bvavra/MIDI_Accordion/Prototypes/Bluetooth/Bluetooth_Tutorial/bluetooth_schematic_1.GIF

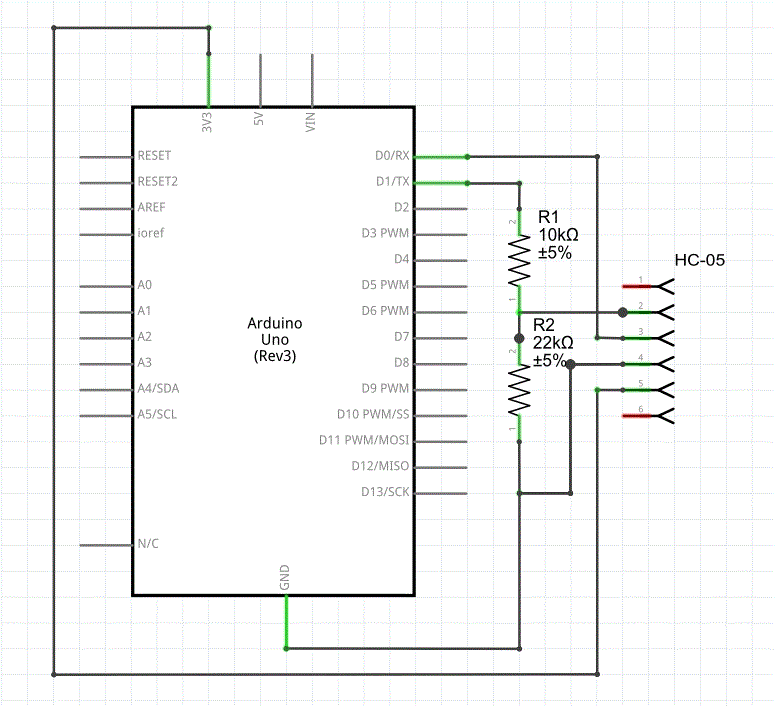
Prototypes/Bluetooth/Bluetooth_Tutorial/bluetooth_schematic_1.GIF
