bvavra/MIDI_Accordion/Prototypes/Opto_Interruptor/Opto_Interruptor_1/working_output.gif

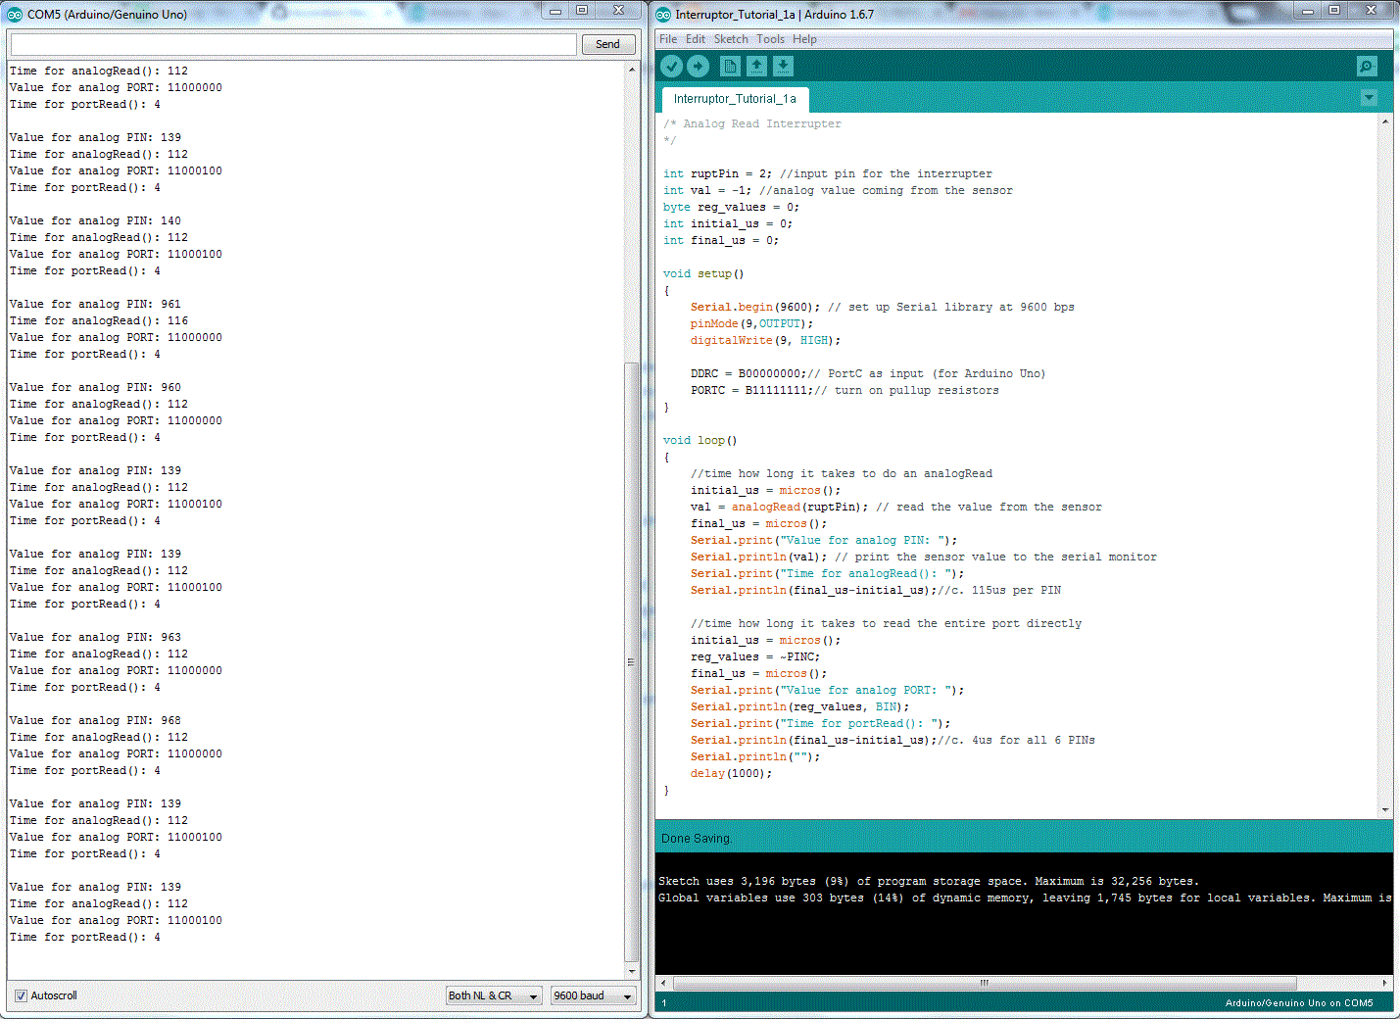
Prototypes/Opto_Interruptor/Opto_Interruptor_1/working_output.gif
