bvavra/MIDI_Accordion/Prototypes/Opto_Interruptor/Opto_Interruptor_1/working_single_analog.GIF

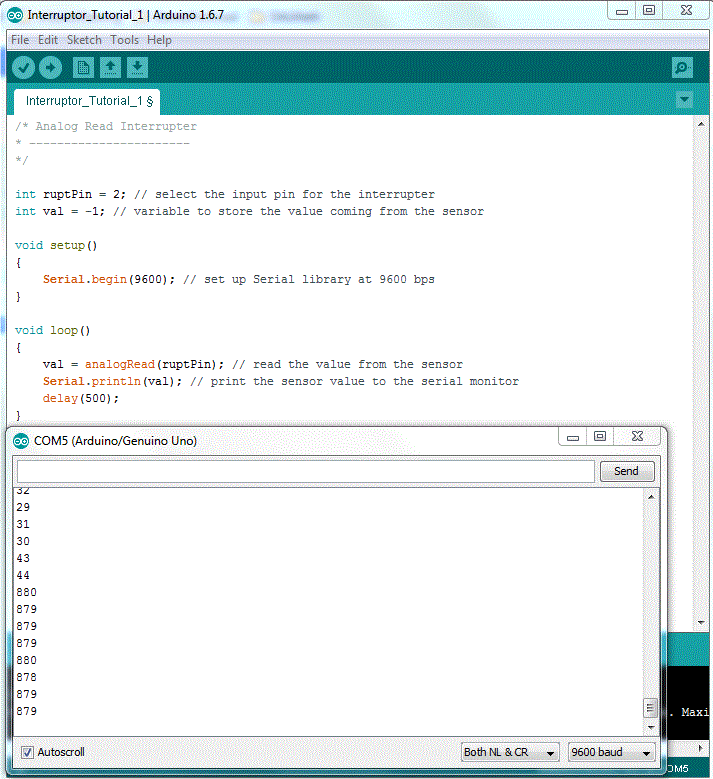
Prototypes/Opto_Interruptor/Opto_Interruptor_1/working_single_analog.GIF
