bvavra/MIDI_Accordion/Prototypes/Bluetooth/Bluetooth_Tutorial/bluetooth_fig1_serial.GIF

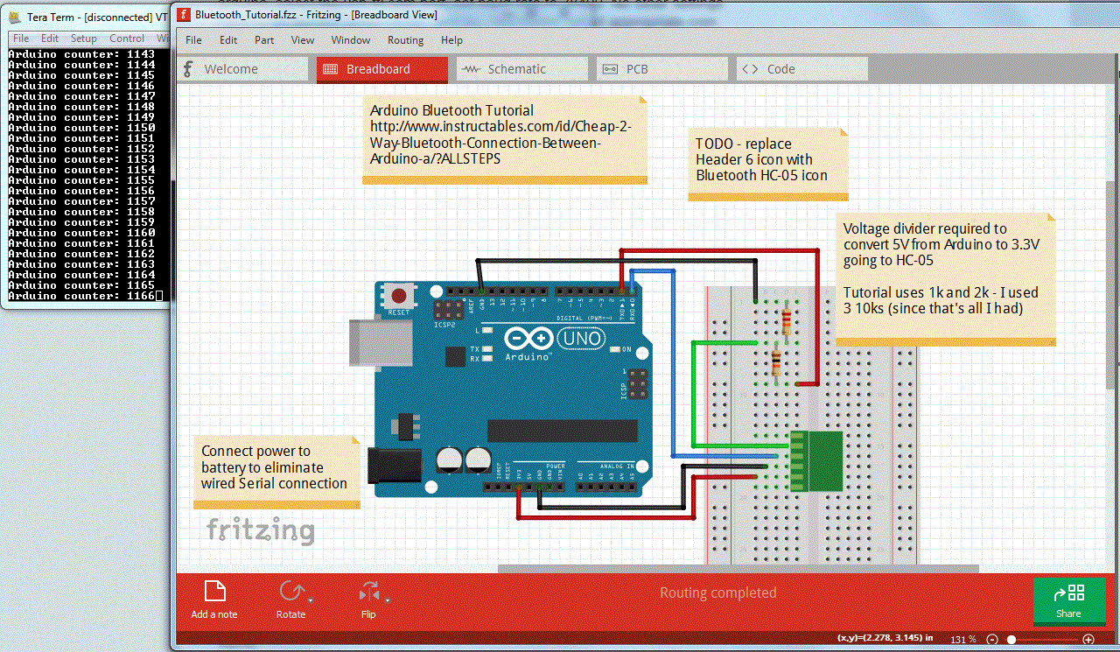
Prototypes/Bluetooth/Bluetooth_Tutorial/bluetooth_fig1_serial.GIF
