bvavra/MIDI_Accordion/Prototypes/Bluetooth/Bluetooth_Tutorial/bluetooth_fig1b_arduino.jpg

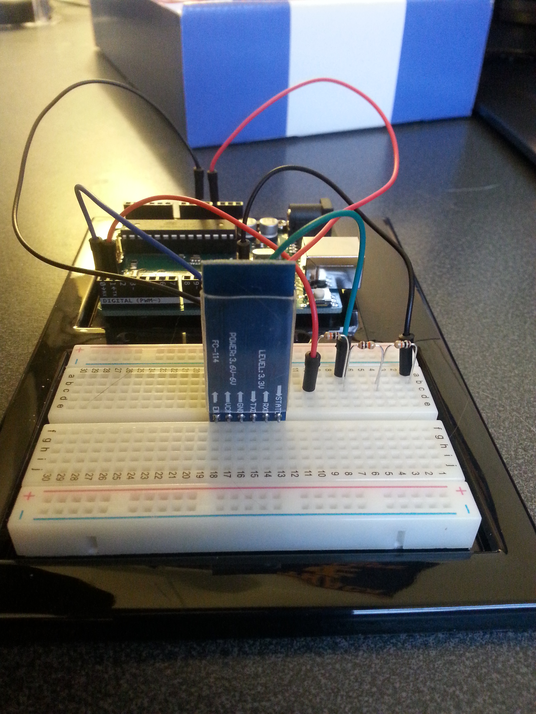
Prototypes/Bluetooth/Bluetooth_Tutorial/bluetooth_fig1b_arduino.jpg
