bvavra/MIDI_Accordion/Prototypes/Bluetooth/Bluetooth_Tutorial_2/bluetooth_fig2_midi.GIF

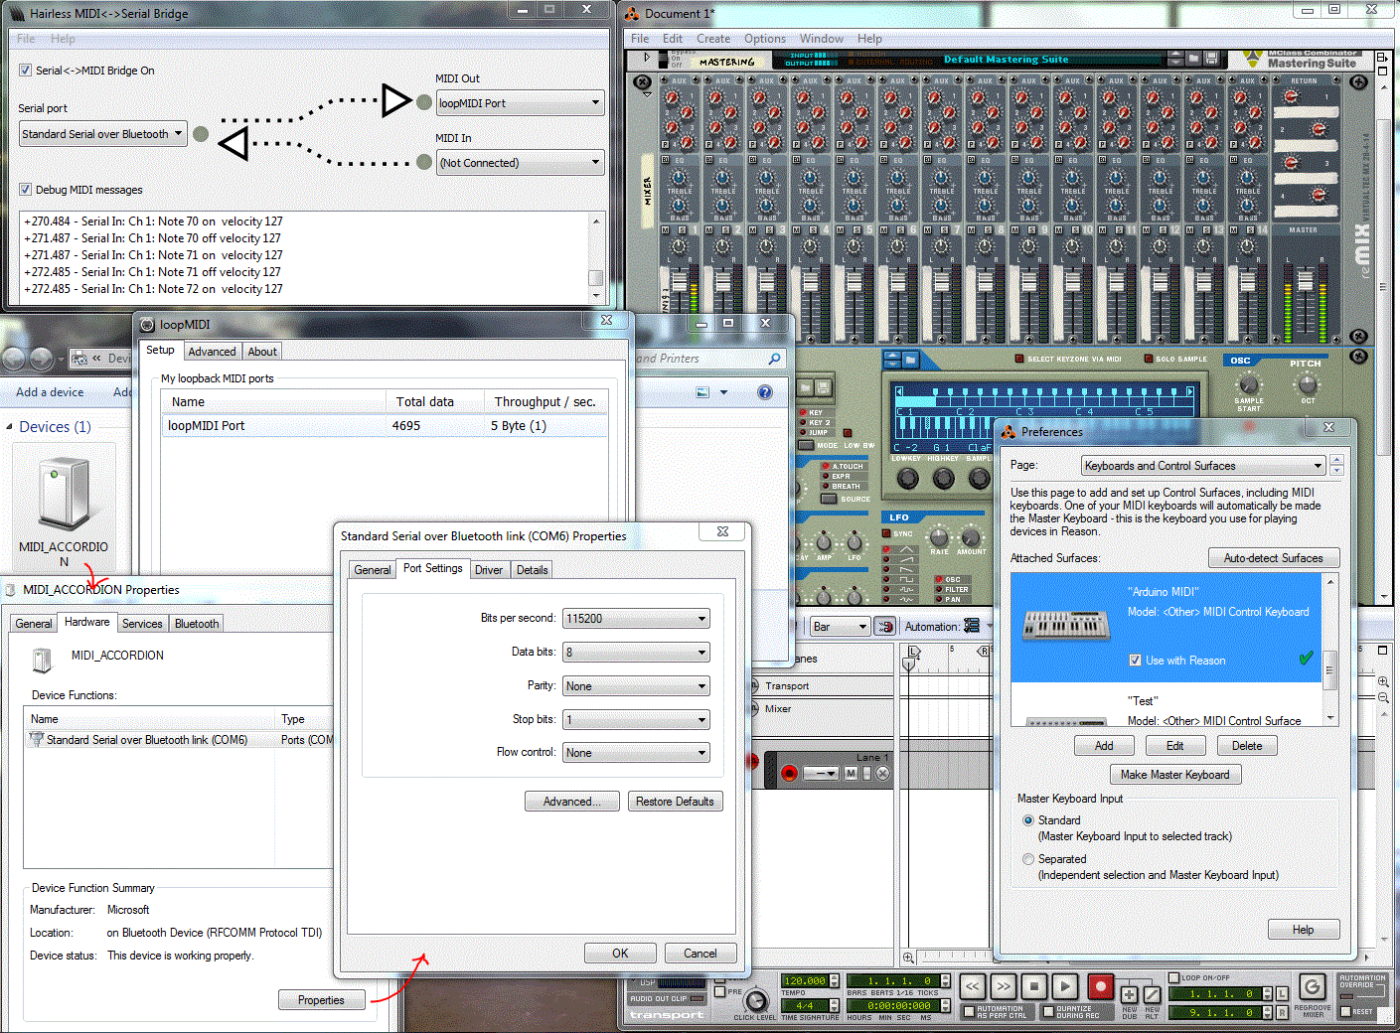
Prototypes/Bluetooth/Bluetooth_Tutorial_2/bluetooth_fig2_midi.GIF
