bvavra/MIDI_Accordion/Prototypes/Bluetooth/Bluetooth_Tutorial_2/bluetooth_fig2a_arduino.jpg

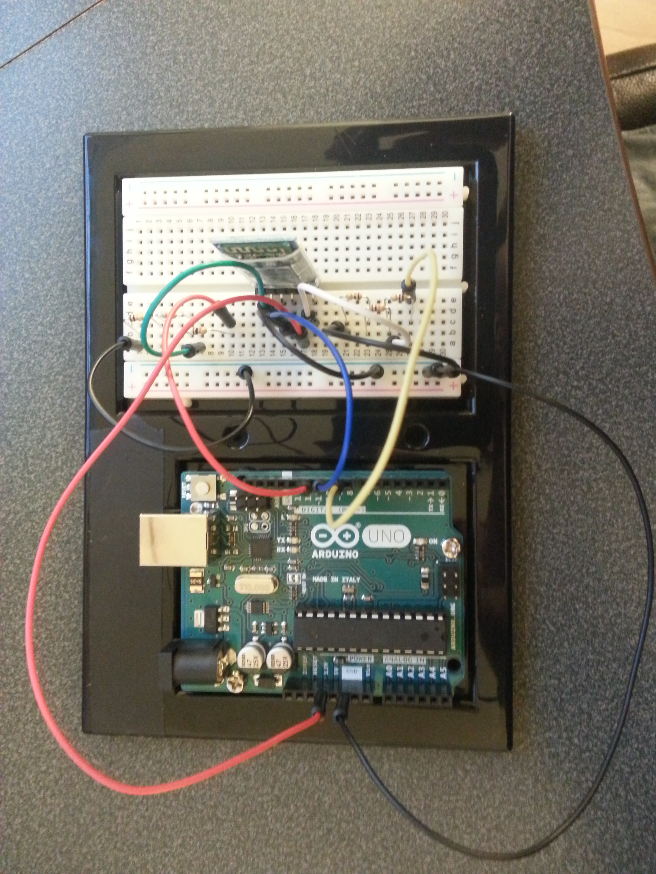
Prototypes/Bluetooth/Bluetooth_Tutorial_2/bluetooth_fig2a_arduino.jpg
