bvavra/MIDI_Accordion/Prototypes/MIDI_Tutorial/midi_fig2_serial_to_midi.GIF

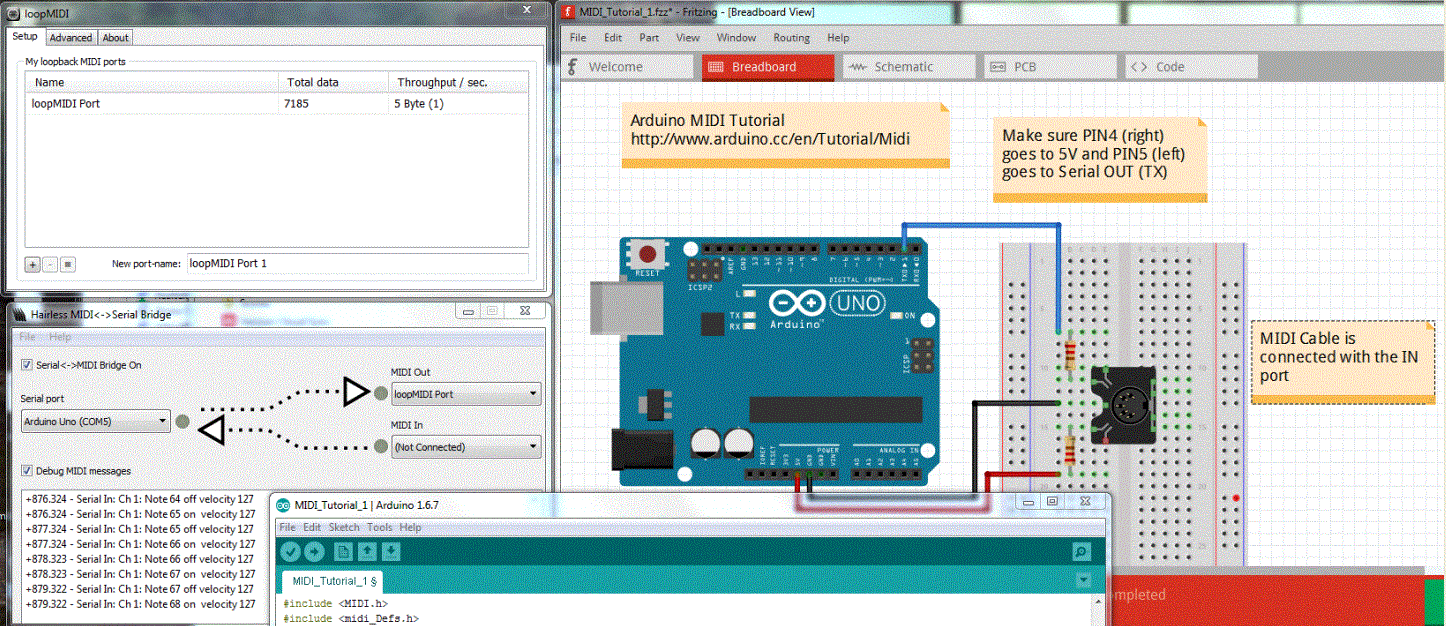
Prototypes/MIDI_Tutorial/midi_fig2_serial_to_midi.GIF
