bvavra/MIDI_Accordion/Prototypes/MIDI_Tutorial/midi_fig3_arduino_to_reason.GIF

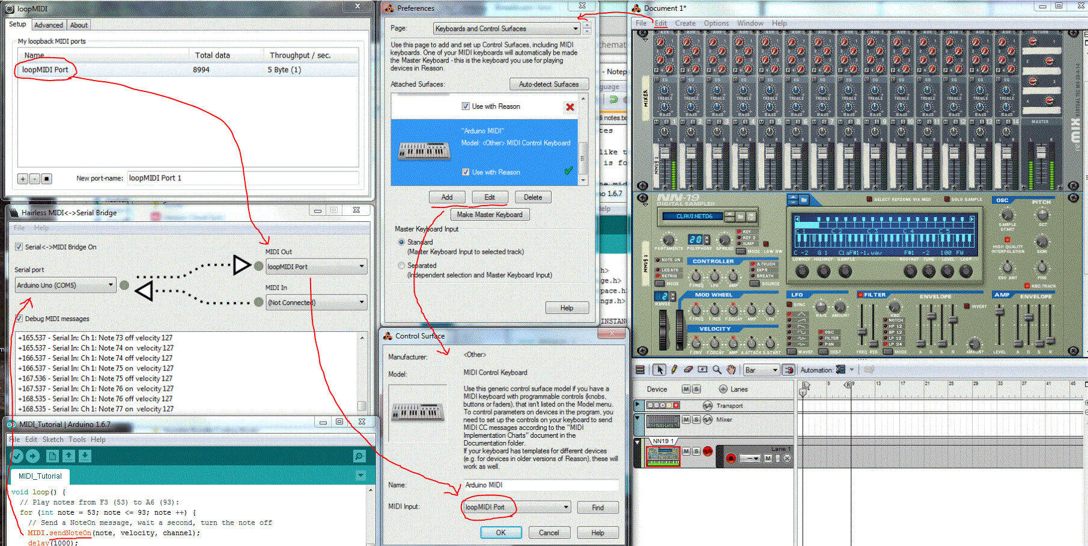
Prototypes/MIDI_Tutorial/midi_fig3_arduino_to_reason.GIF
