bvavra/MIDI_Accordion/Prototypes/MIDI_Tutorial/Virtual_MIDI_Piano_Working.JPG

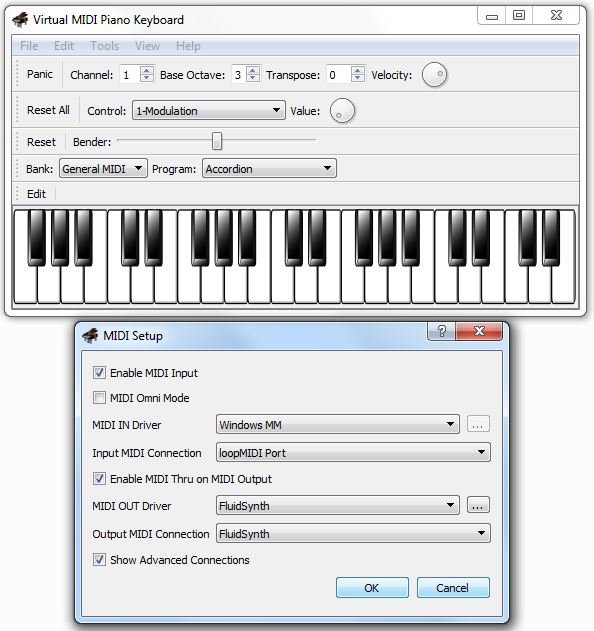
Prototypes/MIDI_Tutorial/Virtual_MIDI_Piano_Working.JPG
